SMotlaq/open-watch/photos/Pic2.JPG

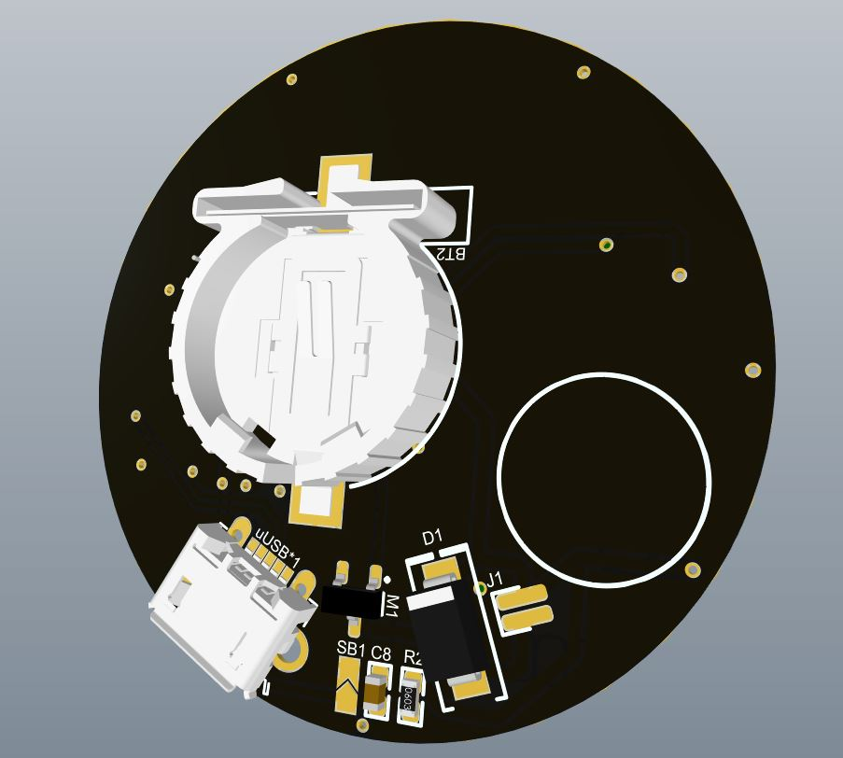
photos/Pic2.JPG
