SMotlaq/open-watch/photos/Pic3.JPG

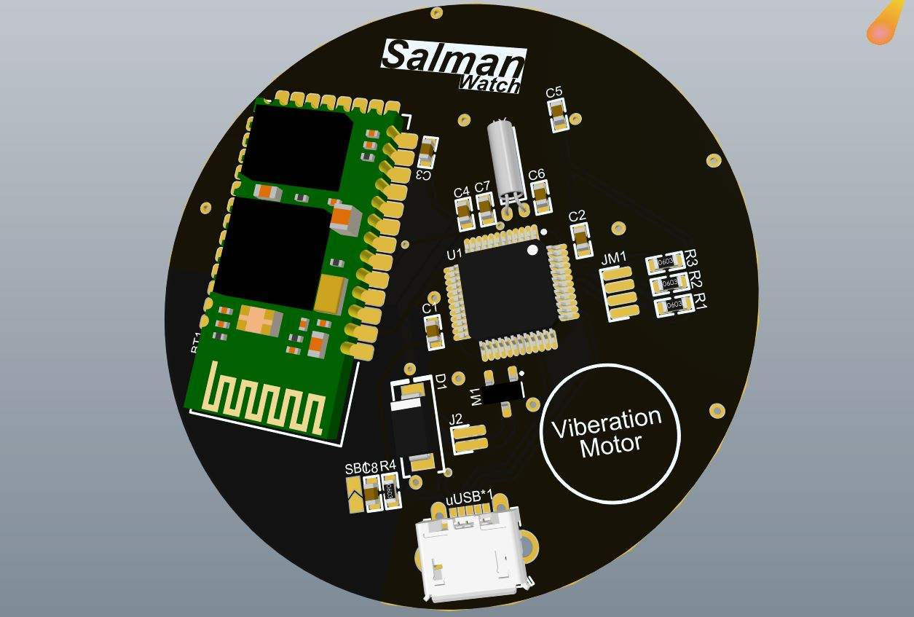
photos/Pic3.JPG
