SMotlaq/open-watch/photos/Pic4.JPG

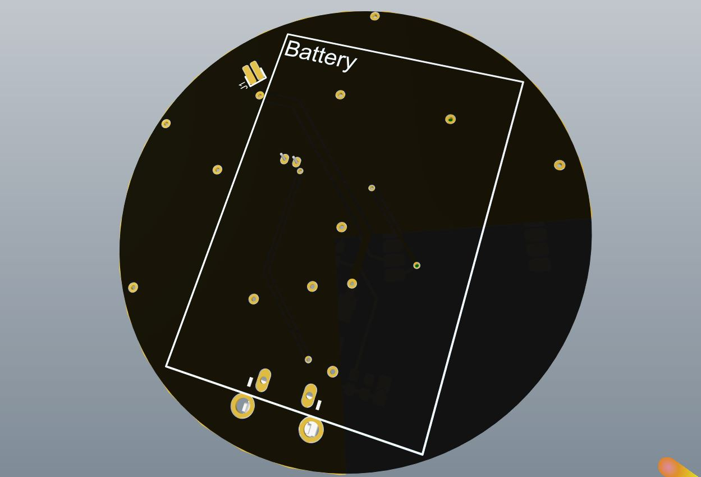
photos/Pic4.JPG
