SMotlaq/open-watch/photos/Pic5.jpg

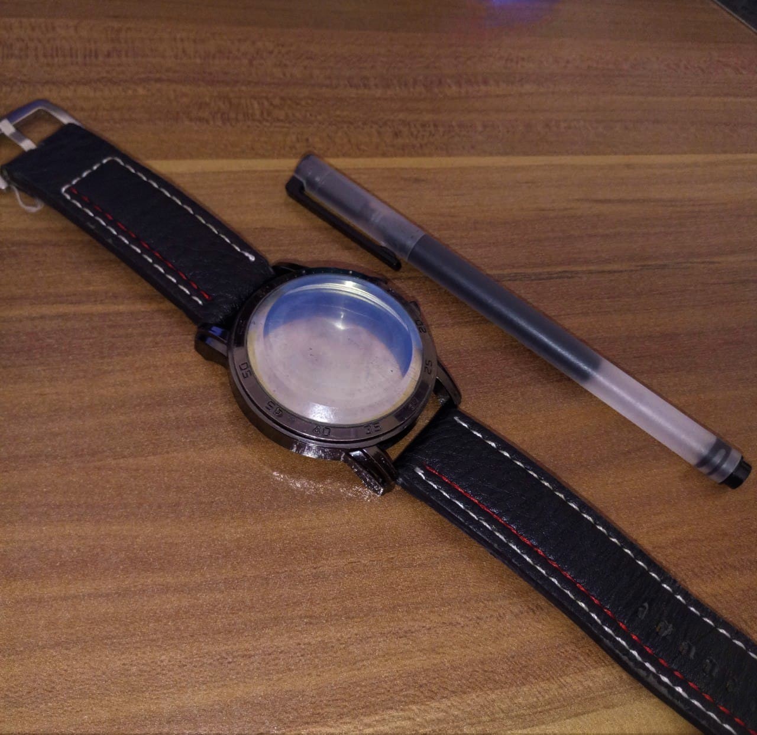
photos/Pic5.jpg
