SMotlaq/open-watch/photos/Pic6.JPG

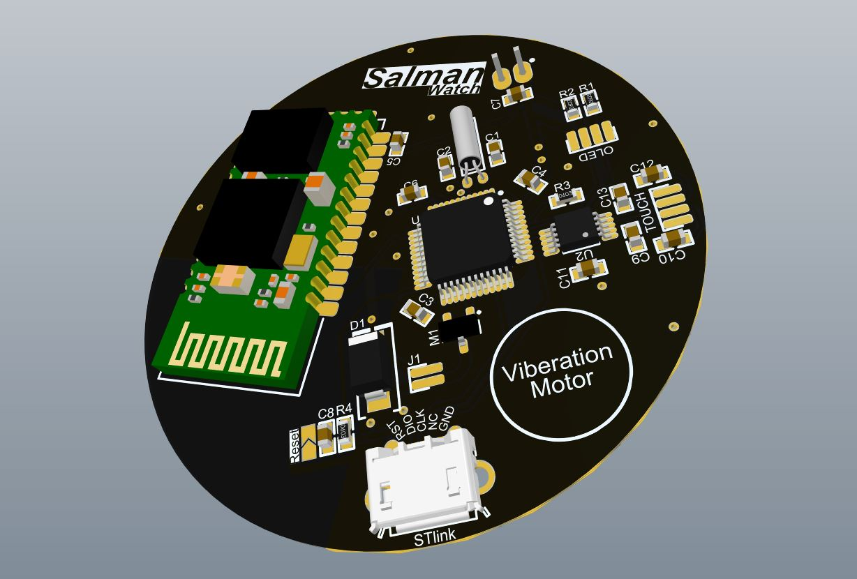
photos/Pic6.JPG
