SMotlaq/open-watch/photos/Pic7.JPG

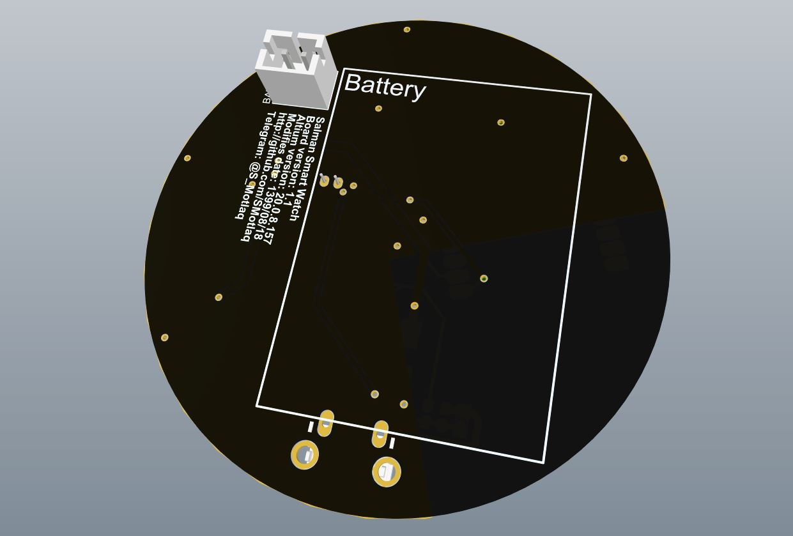
photos/Pic7.JPG
