SMotlaq/open-watch/photos/Pic9.JPG

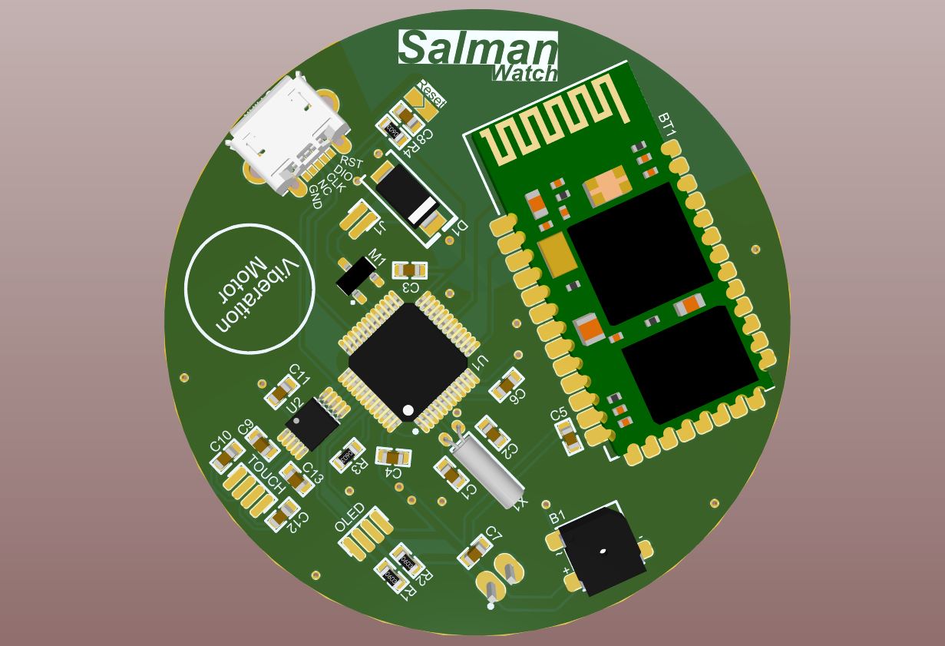
photos/Pic9.JPG
