SMotlaq/open-watch/photos/Pic10.JPG

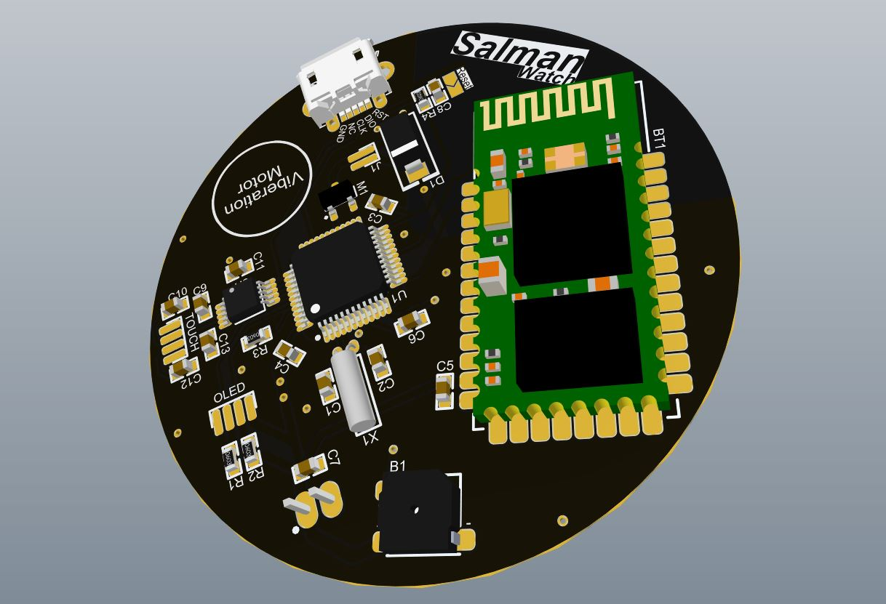
photos/Pic10.JPG
