SMotlaq/open-watch/photos/Pic11.JPG

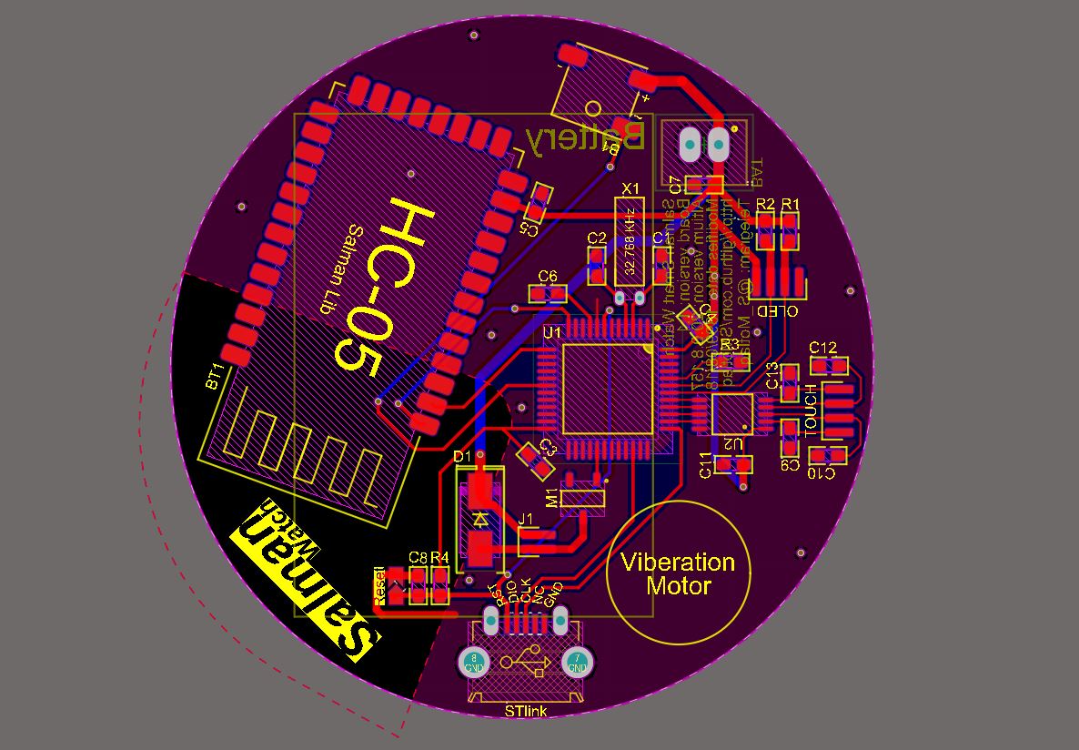
photos/Pic11.JPG
