SMotlaq/open-watch/photos/Pic12.JPG

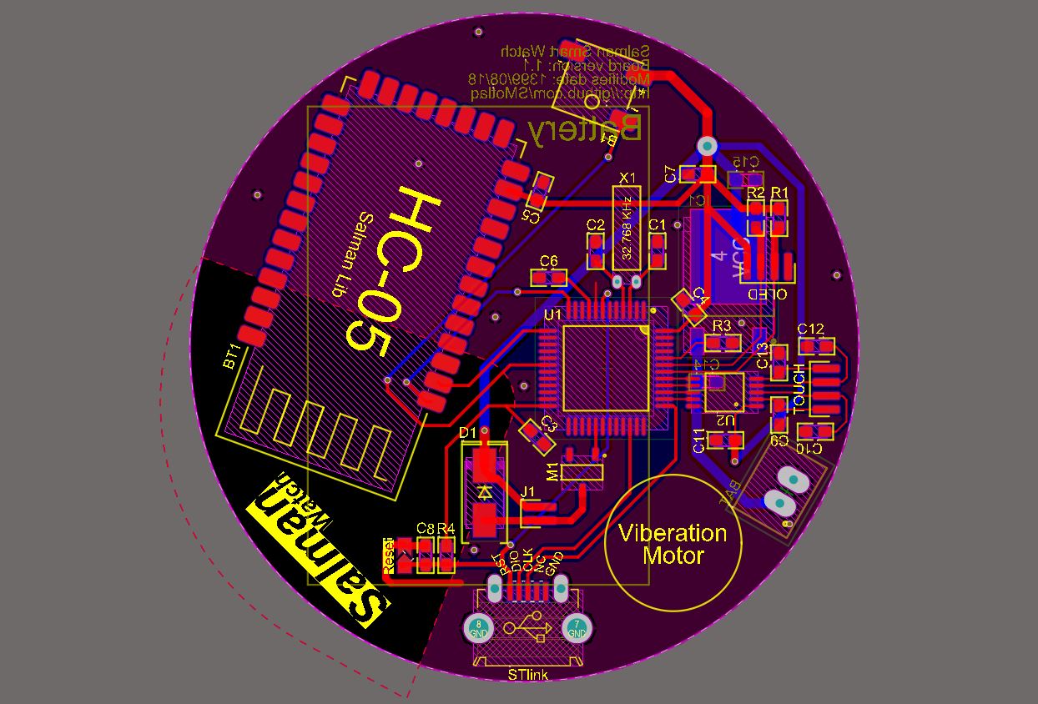
photos/Pic12.JPG
