SMotlaq/open-watch/photos/Pic13.JPG

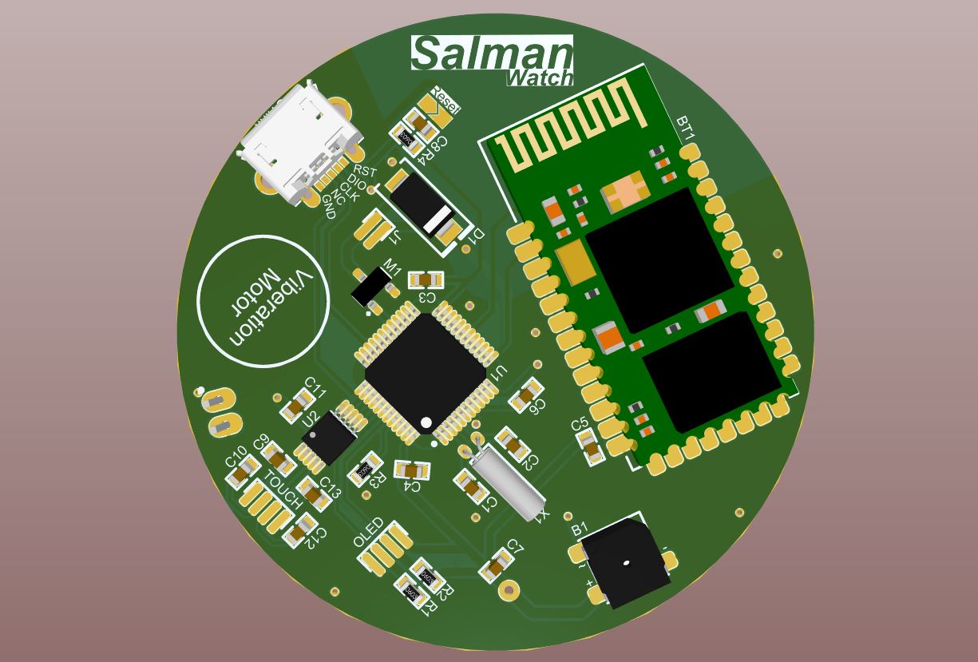
photos/Pic13.JPG
