SMotlaq/open-watch/photos/Pic15.JPG

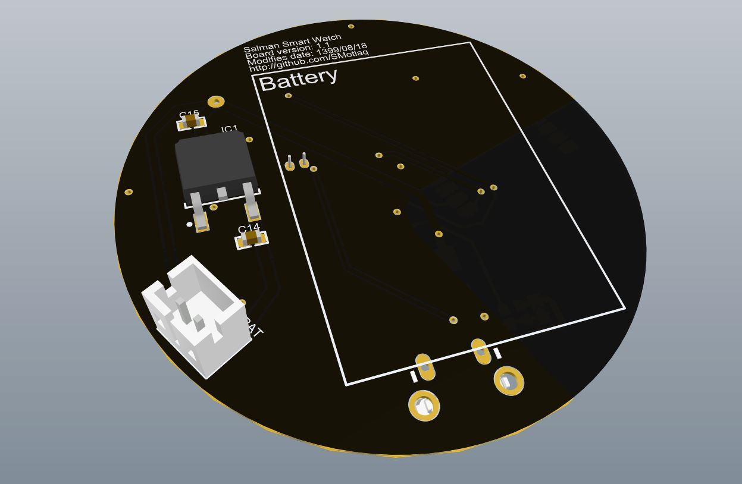
photos/Pic15.JPG
