SMotlaq/open-watch/photos/Pic17.JPG

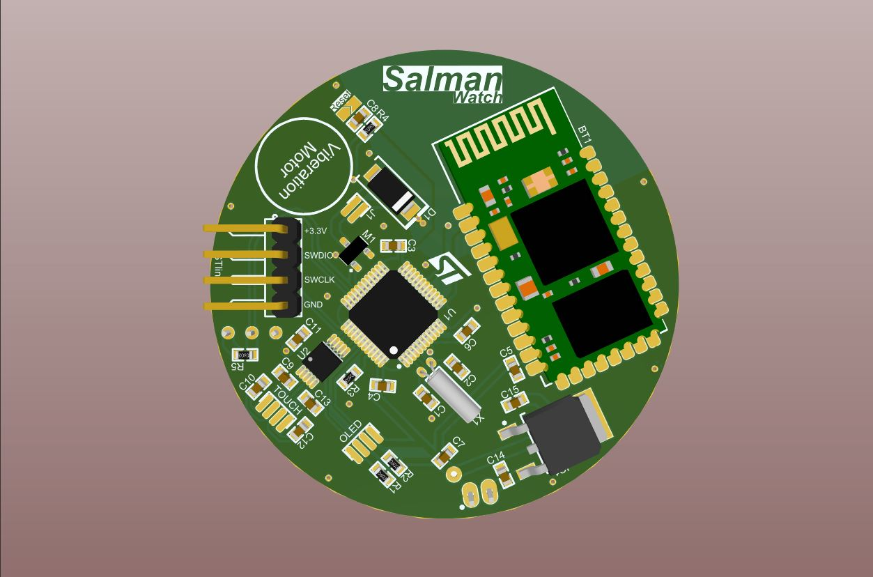
photos/Pic17.JPG
