SMotlaq/open-watch/photos/Pic18.JPG

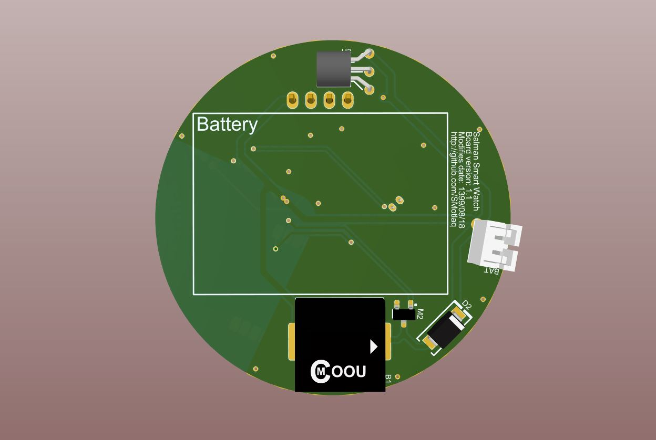
photos/Pic18.JPG
