SMotlaq/open-watch/photos/Pic19.JPG

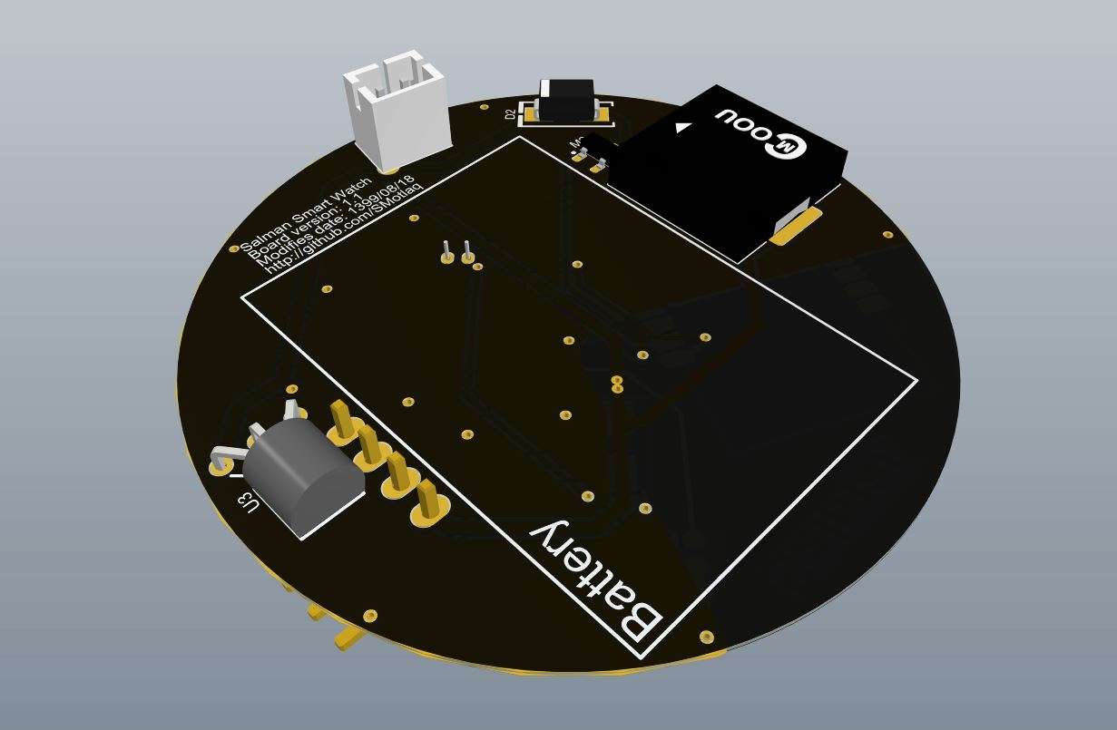
photos/Pic19.JPG
