SMotlaq/open-watch/photos/Pic20.JPG

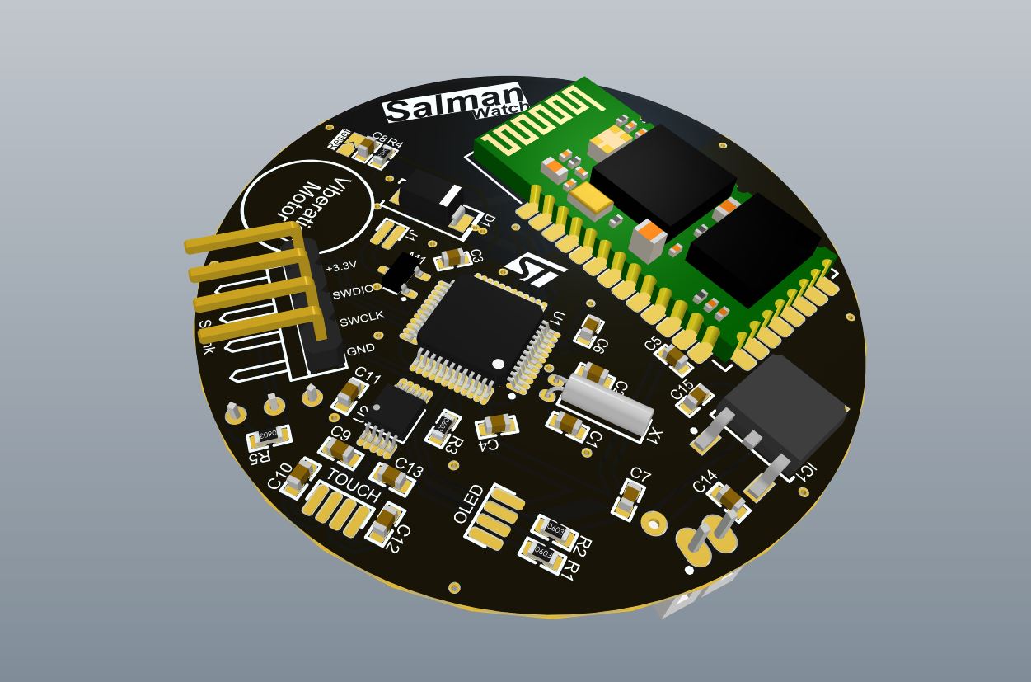
photos/Pic20.JPG
