SMotlaq/open-watch/photos/Pic21.JPG

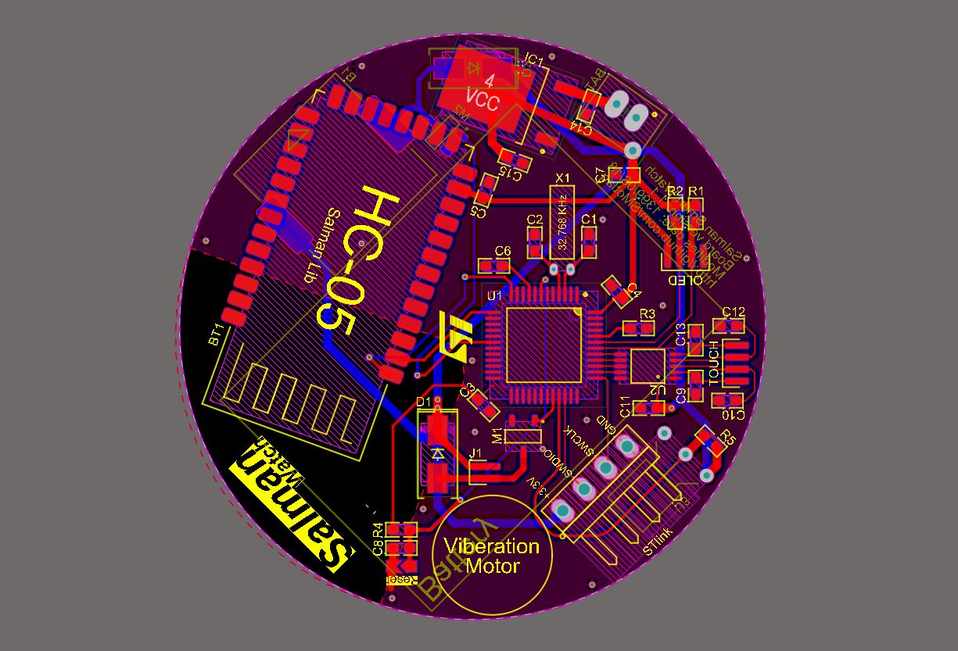
photos/Pic21.JPG
