SMotlaq/open-watch/photos/Pic22.jpg

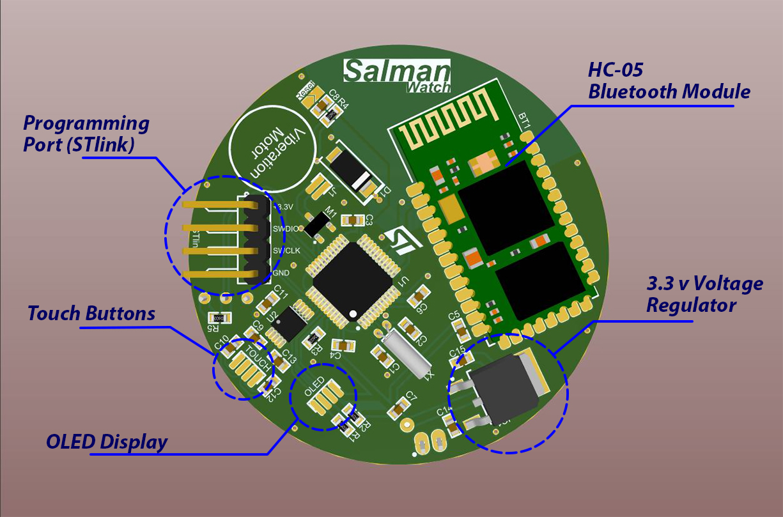
photos/Pic22.jpg
