SMotlaq/open-watch/photos/Pic23.jpg

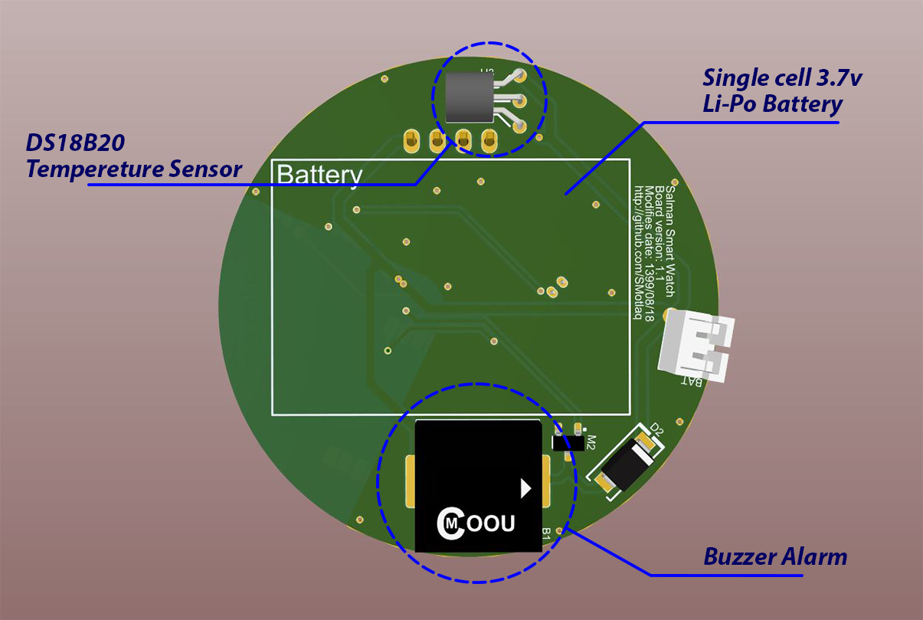
photos/Pic23.jpg
