SMotlaq/open-watch/photos/Pic24.JPG

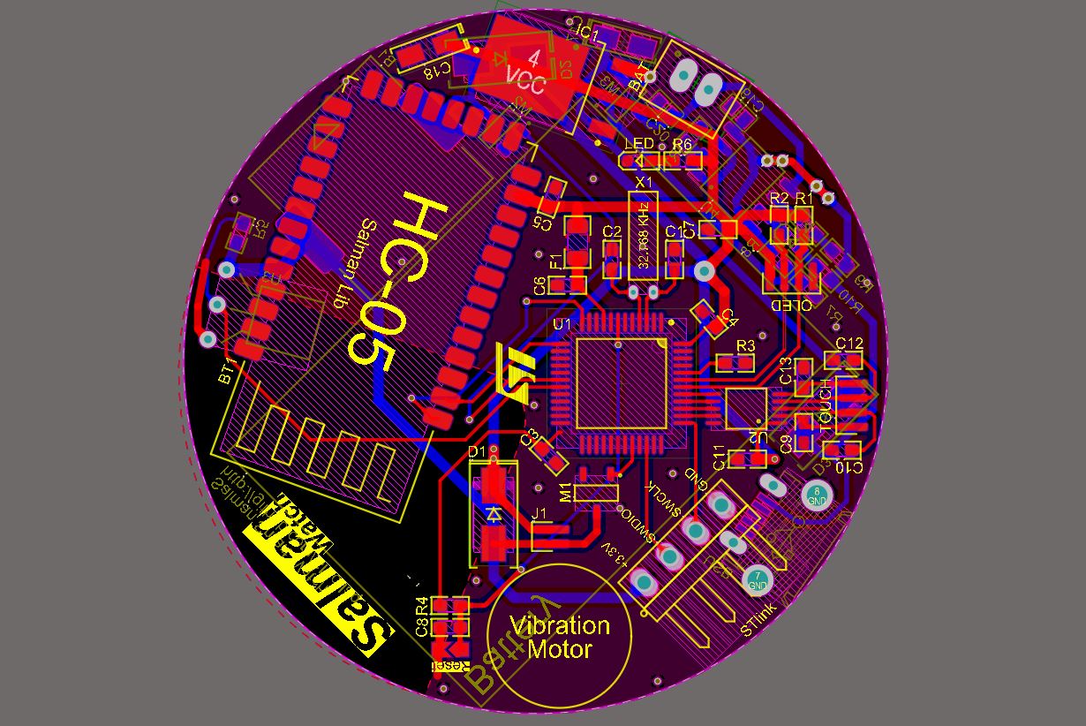
photos/Pic24.JPG
