SMotlaq/open-watch/photos/Pic25.JPG

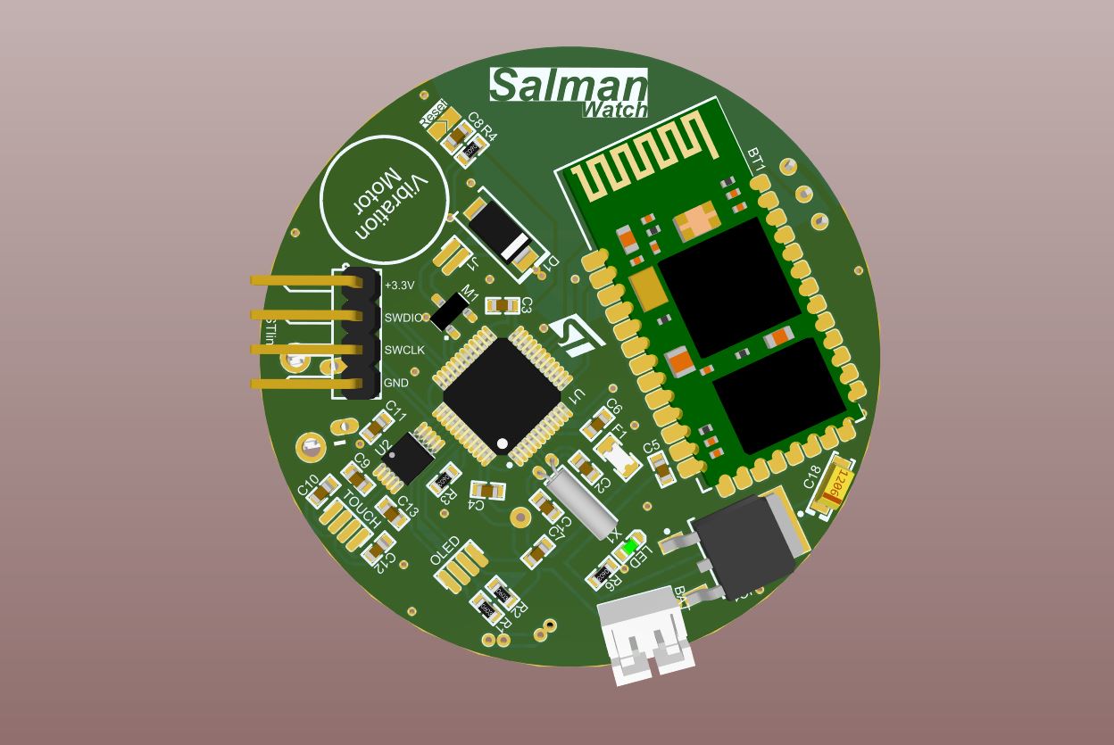
photos/Pic25.JPG
