SMotlaq/open-watch/photos/Pic26.JPG

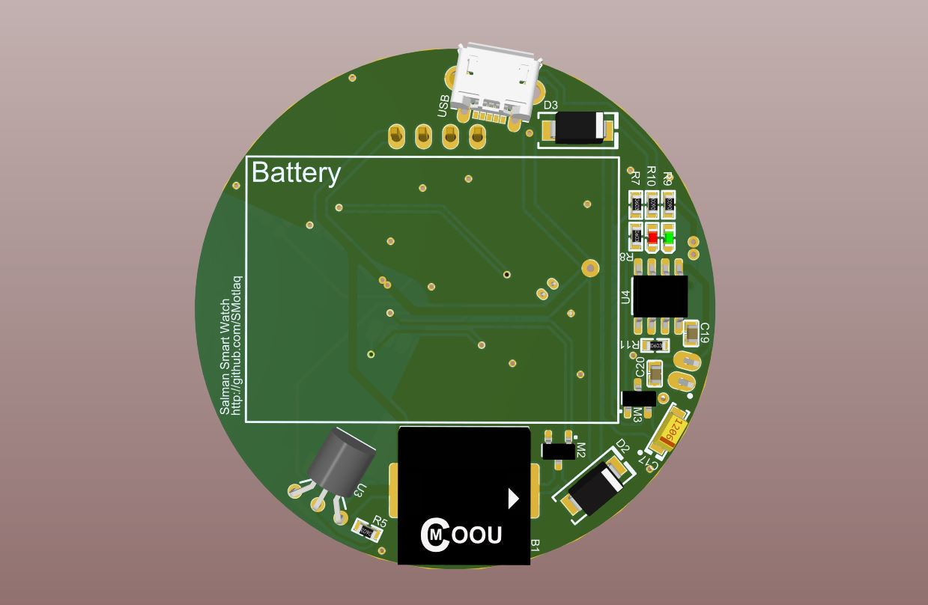
photos/Pic26.JPG
