SMotlaq/open-watch/photos/Pic27.JPG

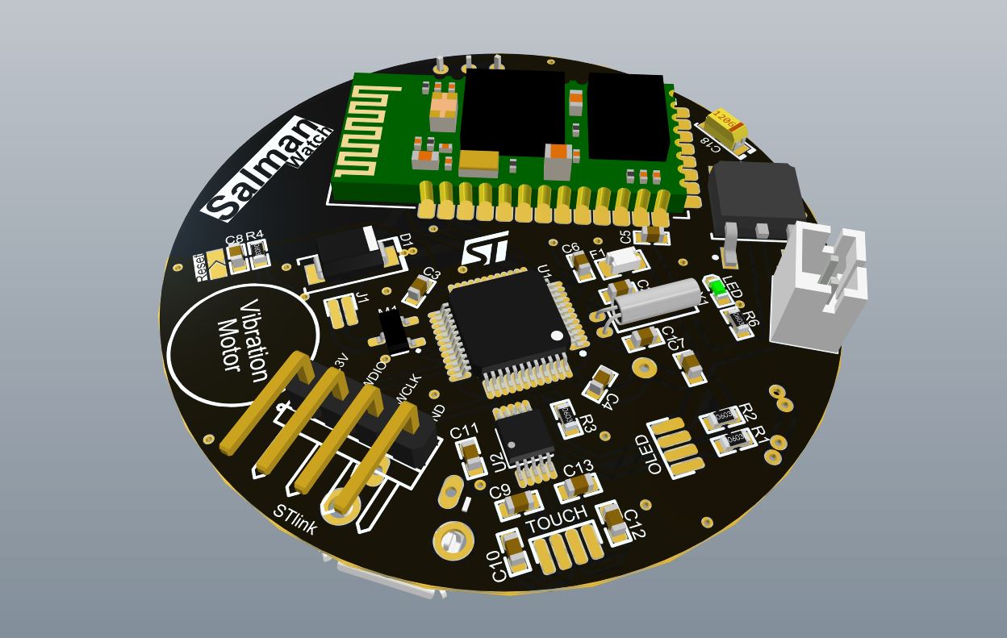
photos/Pic27.JPG
