SMotlaq/open-watch/photos/Pic28.JPG

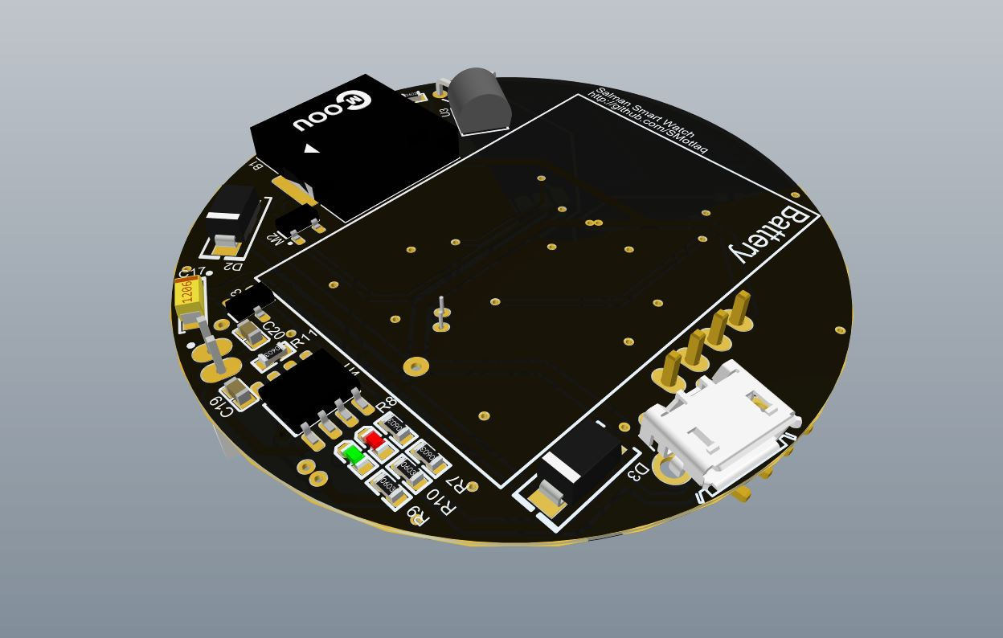
photos/Pic28.JPG
