SMotlaq/open-watch/photos/Pic30.jpg

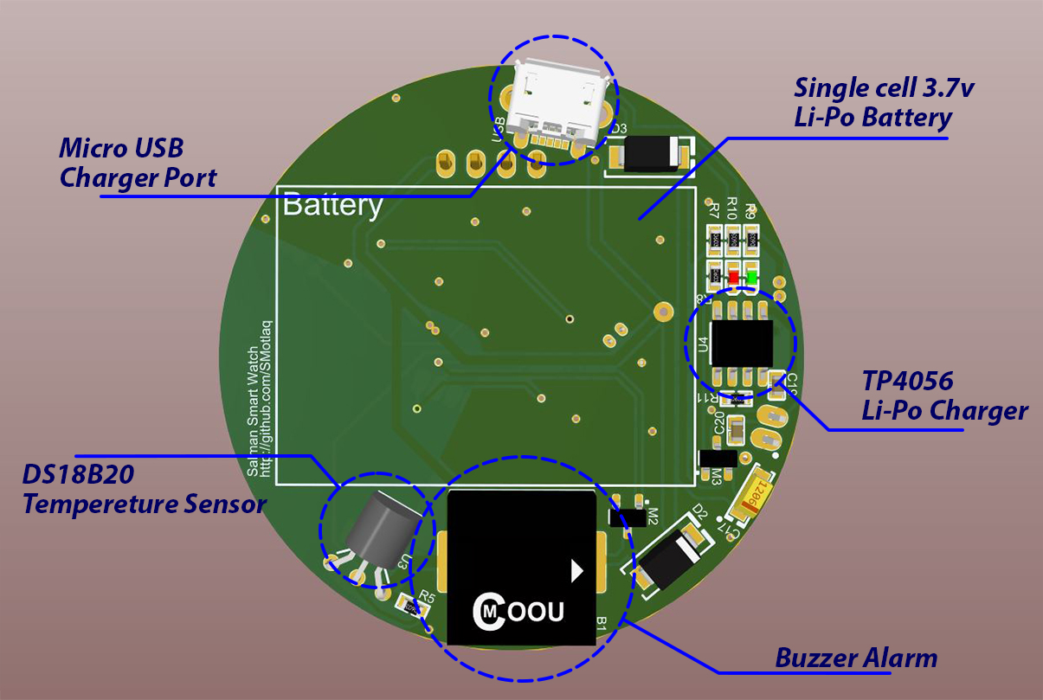
photos/Pic30.jpg
