SMotlaq/open-watch/photos/Pic34.jpg

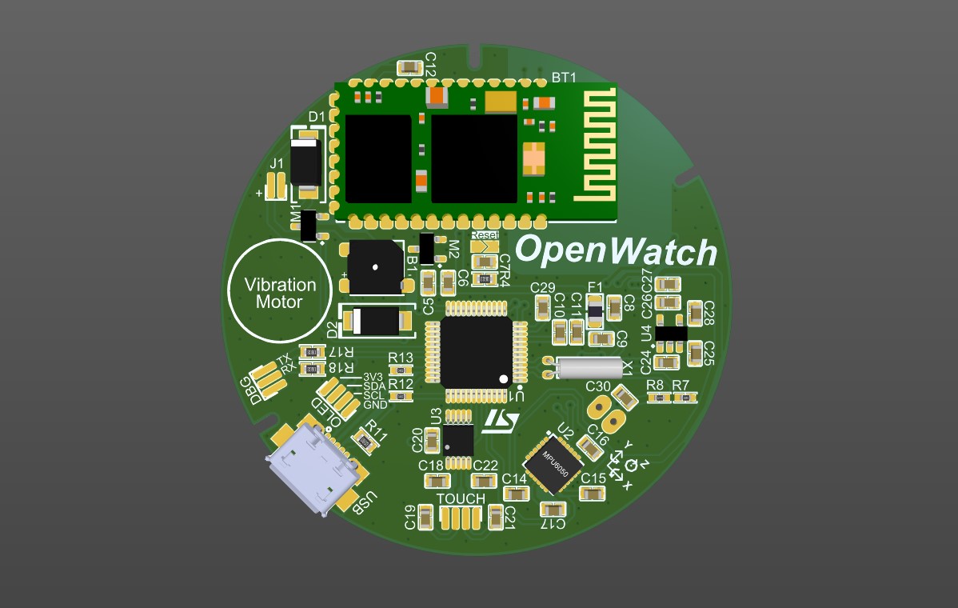
photos/Pic34.jpg
