SMotlaq/open-watch/photos/Pic35.jpg

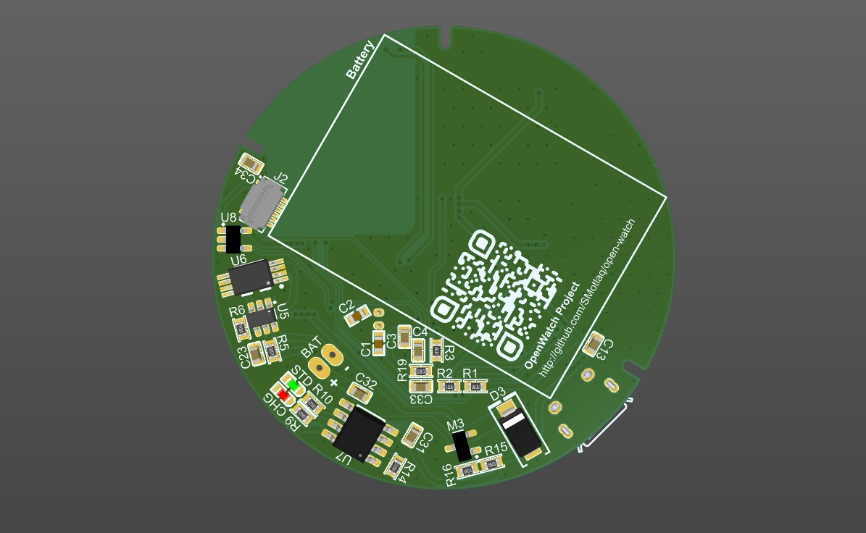
photos/Pic35.jpg
