SMotlaq/open-watch/photos/Pic43.jpg

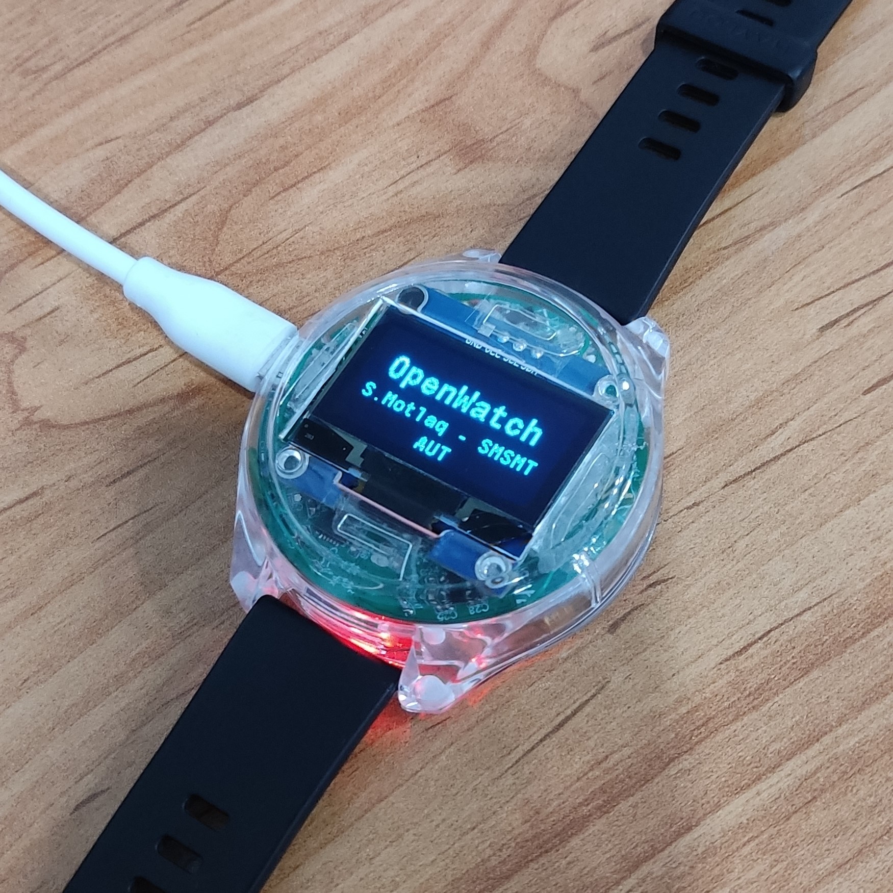
photos/Pic43.jpg
