SMotlaq/open-watch/open-watch-firmware/my_watch_software/MyDrivers/Pages/pages.h

#ifndef __PAGES__
#define __PAGES__

#include "system.h"
#include "ssd1306.h"
#include "stdio.h"
#include "i2c.h"

void render_ack_waiting(System* sys);
void render_home(System* sys);
void render_connected(System* sys);
void render_bloody_hell(System* sys);
void render_pedomedo(System* sys);
void render_about(System* sys);
void render_ringing(System* sys);

#endif
