SMotlaq/open-watch/open-watch-firmware/my_watch_software/MyDrivers/MAX30102/max30102_for_stm32_hal.h

#ifndef MAX30102_FOR_STM32_HAL_H
#define MAX30102_FOR_STM32_HAL_H

#include "main.h"
#include <stdint.h>
#include <stdio.h>
#include <string.h>
#include <stdlib.h>
#include <string.h>

#define MAX30102_I2C_ADDR 0x57
#define MAX30102_I2C_TIMEOUT 1000

#define MAX30102_BYTES_PER_SAMPLE 6
#define MAX30102_SAMPLE_LEN_MAX 32

#define MAX30102_INTERRUPT_STATUS_1 0x00
#define MAX30102_INTERRUPT_STATUS_2 0x01
#define MAX30102_INTERRUPT_ENABLE_1 0x02
#define MAX30102_INTERRUPT_ENABLE_2 0x03
#define MAX30102_INTERRUPT_A_FULL 7
#define MAX30102_INTERRUPT_PPG_RDY 6
#define MAX30102_INTERRUPT_ALC_OVF 5
#define MAX30102_INTERRUPT_DIE_TEMP_RDY 1

#define MAX30102_FIFO_WR_PTR 0x04
#define MAX30102_OVF_COUNTER 0x05
#define MAX30102_FIFO_RD_PTR 0x06

#define MAX30102_FIFO_DATA 0x07

#define MAX30102_FIFO_CONFIG 0x08
#define MAX30102_FIFO_CONFIG_SMP_AVE 5
#define MAX30102_FIFO_CONFIG_ROLL_OVER_EN 4
#define MAX30102_FIFO_CONFIG_FIFO_A_FULL 0

#define MAX30102_MODE_CONFIG 0x09
#define MAX30102_MODE_SHDN 7
#define MAX30102_MODE_RESET 6
#define MAX30102_MODE_MODE 0

#define MAX30102_SPO2_CONFIG 0x0a
#define MAX30102_SPO2_ADC_RGE 5
#define MAX30102_SPO2_SR 2
#define MAX30102_SPO2_LEW_PW 0

#define MAX30102_LED_IR_PA1 0x0c
#define MAX30102_LED_RED_PA2 0x0d

#define MAX30102_MULTI_LED_CTRL_1 0x11
#define MAX30102_MULTI_LED_CTRL_SLOT2 4
#define MAX30102_MULTI_LED_CTRL_SLOT1 0
#define MAX30102_MULTI_LED_CTRL_2 0x12
#define MAX30102_MULTI_LED_CTRL_SLOT4 4
#define MAX30102_MULTI_LED_CTRL_SLOT3 0

#define MAX30102_DIE_TINT 0x1f
#define MAX30102_DIE_TFRAC 0x20
#define MAX30102_DIE_TFRAC_INCREMENT 0.0625f
#define MAX30102_DIE_TEMP_CONFIG 0x21
#define MAX30102_DIE_TEMP_EN 1

typedef enum max30102_mode_t
{
    max30102_heart_rate = 0x02,
    max30102_spo2 = 0x03,
    max30102_multi_led = 0x07
} max30102_mode_t;

typedef enum max30102_smp_ave_t
{
    max30102_smp_ave_1,
    max30102_smp_ave_2,
    max30102_smp_ave_4,
    max30102_smp_ave_8,
    max30102_smp_ave_16,
    max30102_smp_ave_32,
} max30102_smp_ave_t;

typedef enum max30102_sr_t
{
    max30102_sr_50,
    max30102_sr_100,
    max30102_sr_200,
    max30102_sr_400,
    max30102_sr_800,
    max30102_sr_1000,
    max30102_sr_1600,
    max30102_sr_3200
} max30102_sr_t;

typedef enum max30102_led_pw_t
{
    max30102_pw_15_bit,
    max30102_pw_16_bit,
    max30102_pw_17_bit,
    max30102_pw_18_bit
} max30102_led_pw_t;

typedef enum max30102_adc_t
{
    max30102_adc_2048,
    max30102_adc_4096,
    max30102_adc_8192,
    max30102_adc_16384
} max30102_adc_t;

typedef enum max30102_multi_led_ctrl_t
{
    max30102_led_off,
    max30102_led_red,
    max30102_led_ir
} max30102_multi_led_ctrl_t;

typedef struct max30102_t
{
    I2C_HandleTypeDef *_ui2c;
    uint32_t _ir_samples[32];
    uint32_t _red_samples[32];
    uint8_t _interrupt_flag;
} max30102_t;

__weak void max30102_plot(uint32_t ir_sample, uint32_t red_sample);

void max30102_init(max30102_t *obj, I2C_HandleTypeDef *hi2c);
void max30102_write(max30102_t *obj, uint8_t reg, uint8_t *buf, uint16_t buflen);
void max30102_read(max30102_t *obj, uint8_t reg, uint8_t *buf, uint16_t buflen);

void max30102_reset(max30102_t *obj);

void max30102_set_a_full(max30102_t *obj, uint8_t enable);
void max30102_set_ppg_rdy(max30102_t *obj, uint8_t enable);
void max30102_set_alc_ovf(max30102_t *obj, uint8_t enable);
void max30102_set_die_temp_rdy(max30102_t *obj, uint8_t enable);
void max30102_set_die_temp_en(max30102_t *obj, uint8_t enable);

void max30102_on_interrupt(max30102_t *obj);
uint8_t max30102_has_interrupt(max30102_t *obj);
void max30102_interrupt_handler(max30102_t *obj);

void max30102_shutdown(max30102_t *obj, uint8_t shdn);

void max30102_set_mode(max30102_t *obj, max30102_mode_t mode);
void max30102_set_sampling_rate(max30102_t *obj, max30102_sr_t sr);

void max30102_set_led_pulse_width(max30102_t *obj, max30102_led_pw_t pw);
void max30102_set_adc_resolution(max30102_t *obj, max30102_adc_t adc);

void max30102_set_led_current_1(max30102_t *obj, float ma);
void max30102_set_led_current_2(max30102_t *obj, float ma);
void max30102_set_multi_led_slot_1_2(max30102_t *obj, max30102_multi_led_ctrl_t slot1, max30102_multi_led_ctrl_t slot2);
void max30102_set_multi_led_slot_3_4(max30102_t *obj, max30102_multi_led_ctrl_t slot3, max30102_multi_led_ctrl_t slot4);

void max30102_set_fifo_config(max30102_t *obj, max30102_smp_ave_t smp_ave, uint8_t roll_over_en, uint8_t fifo_a_full);
void max30102_clear_fifo(max30102_t *obj);
void max30102_read_fifo(max30102_t *obj);

void max30102_read_temp(max30102_t *obj, int8_t *temp_int, uint8_t *temp_frac);

#endif
